gwyatt40/PID-Motor-Control/MotorControlMrHTest/MotorControlCode-MrH test.ino

int potPin= 2;  //Sets potentiometer to analog pin A0
int AC_LOAD= 3;  // Sets AC LOAD pin as 3 
int potValue;  // Variable read from potentiometer
int dimValue; // Dim amount variable 



unsigned char dimming = 128; // Dimming level (0-128) 0 = ON, 128 = OFF
 
void setup() {
  pinMode(potPin, INPUT);  //Potentiometer pin is InPuT
  pinMode(AC_LOAD, OUTPUT); //AC LOAD pin is output
  Serial.begin(9600);      
  attachInterrupt(6, zero_crosss_int, RISING); // Choose the zero cross interrupt # from the table above
}

void zero_crosss_int() {

int dimtime = (65*(int)dimming); // For 60Hz =>65
delayMicroseconds(dimtime); // Wait till firing the TRIAC
digitalWrite(AC_LOAD, HIGH); // Fire the TRIAC 
delayMicroseconds(10); // triac On propogation dely
// (for 60Hz use 8.33) Some Triacs need a longer period
digitalWrite(AC_LOAD, LOW); 

}

void loop() {
  
 potValue = analogRead(potPin);  //readValue derived from reading the potentiometer value
 dimValue= potValue/8; //Formula for calculating dim value

 Serial.print("You are writing a value of ");  
 Serial.println(dimValue); //serial print for debugging purposes

 for (int i=5; i <= 126; i++){
 if (dimming < dimValue)
 	dimming++;
if (dimming > dimValue)
 	dimming--;

// dimming= dimValue;
 delay(10);
}
 
}
